Ruwen14/P-Stromerfassung-Kettensaege/Simulation/ADA4098-1.asc

R1: res; 1.25k
R2: res; 5k
R3: res; 1.25k
R4: res; 5k
U1: ADA4098-1
V1: voltage; 5
Vin: voltage; SINE(0 10 2k)
Vref: voltage; 2.5
Named nets: 0, V+, OUT
.tran 2000u
