Ruwen14/P-Stromerfassung-Kettensaege/Simulation/Differenzverstärker_Variante2.asc

L1: ind; 100µ; Rser=2.38
R1: res; 10k
R2: res; 10k
R5: res; 10k
R6: res; 10k
R_d5: res; 2k
R_d6: res; 2k
R_d7: res; 50k
R_d8: res; 50k
RShunt1: res; 0.02
U3: NE5532
U5: NE5532
U6: NE5532
V2: voltage; 15
V3: voltage; PULSE(0 24 0 30n 30n {period * dutyCycle} {period}); AC 1
V4: voltage; 15
Named nets: 0, PWM, -Vcc, Vcc
.tran 5ms
PWM-Auslegung:
Tperiod = 1/f = 1/20kHz = 0.05ms
Ton = DutyCycle * Tperiod = 0.5 * 0.05ms = 0.025ms
.param freq=20k period=1/freq dutyCycle=1.0
Differenzverstärker --> V=20
