Ruwen14/P-Stromerfassung-Kettensaege/Simulation/FullSimulation_MitDifferenzvertärkerVariante1.asc

C1: cap; 27n
D1: diode; 1N4148
D2: diode; 1N4148
D3: diode; 1N4148
D4: diode; 1N4148
D5: diode; 1N4148
D6: diode; 1N4148
D7: diode; 1N4148
D8: diode; 1N4148
Motorspule1: ind; 100µ; Rser=2.38
Motorspule2: ind; 100µ; Rser=2.38
Motorspule3: ind; 100µ; Rser=2.38
R1: res; 20k
R2: res; 20k
R3: res; 20k
R4: res; 100k
R5: res; 5k
R6: res; 10k
R7: res; 100k
R8: res; 36k
R9: res; 36k
R10: res; 25k
R11: res; 25k
R12: res; 10k
R_d1: res; 2.4k
R_d2: res; 2.4k
R_d3: res; 30k
R_d4: res; 30k
R_d5: res; 2.4k
R_d6: res; 2.4k
R_d7: res; 30k
R_d8: res; 30k
R_d9: res; 2.4k
R_d10: res; 2.4k
R_d11: res; 30k
R_d12: res; 30k
R_gr1: res; 20k
R_gr2: res; 20k
R_gr3: res; 20k
R_gr4: res; 10k
R_gr5: res; 20k
R_gr6: res; 20k
R_gr7: res; 20k
R_gr8: res; 20k
R_gr9: res; 10k
R_gr10: res; 20k
R_gr11: res; 20k
R_gr12: res; 20k
R_gr13: res; 20k
R_gr14: res; 10k
R_gr15: res; 20k
Rfb1: res; 20k
Ri1: res; 20k
Ri2: res; 20k
RShunt1: res; 0.02
RShunt2: res; 0.02
RShunt3: res; 0.02
U1: ADA4098-1
U2: NE5532
U3: NE5532
U4: NE5532
U5: NE5532
U6: ADA4098-1
U7: ADA4098-1
U8: NE5532
U9: NE5532
U10: NE5532
U11: NE5532
U12: NE5532
V2: voltage; 15
V3: voltage; 15
V5: voltage; PULSE(0 24 0 30n 30n {period * dutyCycle} {period}); AC 1
Named nets: 0, Vcc, -Vcc, UShuntVerstärkt, Ubetrag, PWM, UShuntVerstärkt2, Ubetrag2, UShuntVerstärkt3, Ubetrag3, Kompensation, Gesamt
.tran 5m
PWM-Auslegung:
Tperiod = 1/f = 1/20kHz = 0.05ms
Ton = DutyCycle * Tperiod = 0.5 * 0.05ms = 0.025ms
Differenzverstärker
Vollweggleichrichter
Differenzverstärker
Vollweggleichrichter
Vollweggleichrichter
Summierverstärker
invertierender (Verstärker)
.param freq=20k period=1/freq dutyCycle=1.0
Messpuntk
Messpuntk2
Messpuntk3
;.ac oct 100 0.1 10000k
Im Schaltplan wurde an dieser Stelle ein Poti zur 
variablen Verstärkung/Abschwächung zstzl. eingefügt
Phase ohne Strom
